grodansparadis/can4vscp-frankfurt-usb/eagle/dsub/Gerbers/frankfurt_usb_pac_rev_c_txt_small.png

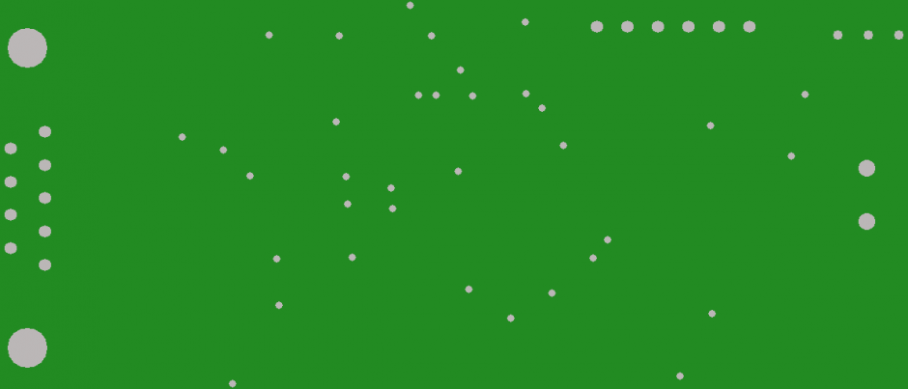
eagle/dsub/Gerbers/frankfurt_usb_pac_rev_c_txt_small.png
