grodansparadis/can4vscp-frankfurt-usb/docs/usb2can.pdf

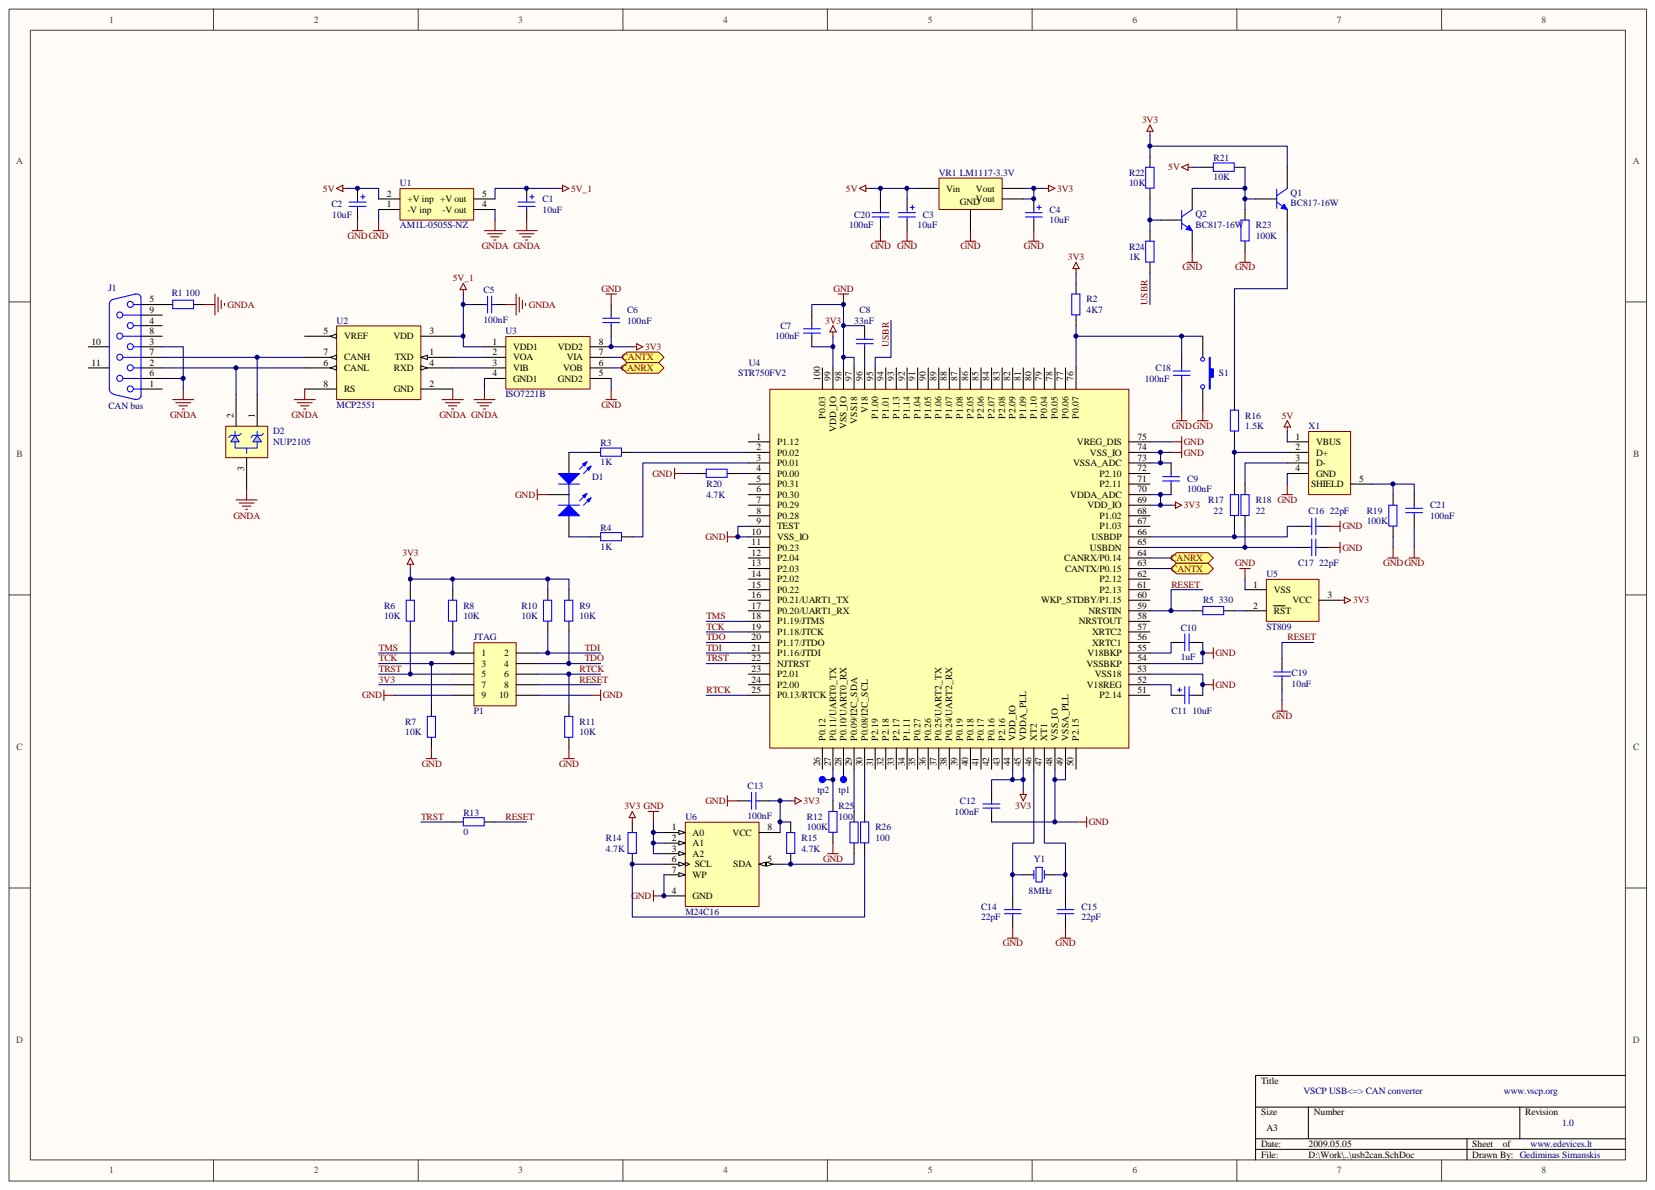
[picture p16: page 1]

VSCP USB<=> CAN converter
